SebG3D/TapePuller/docs/servo/servo_mod/servo_mod_6.jpg

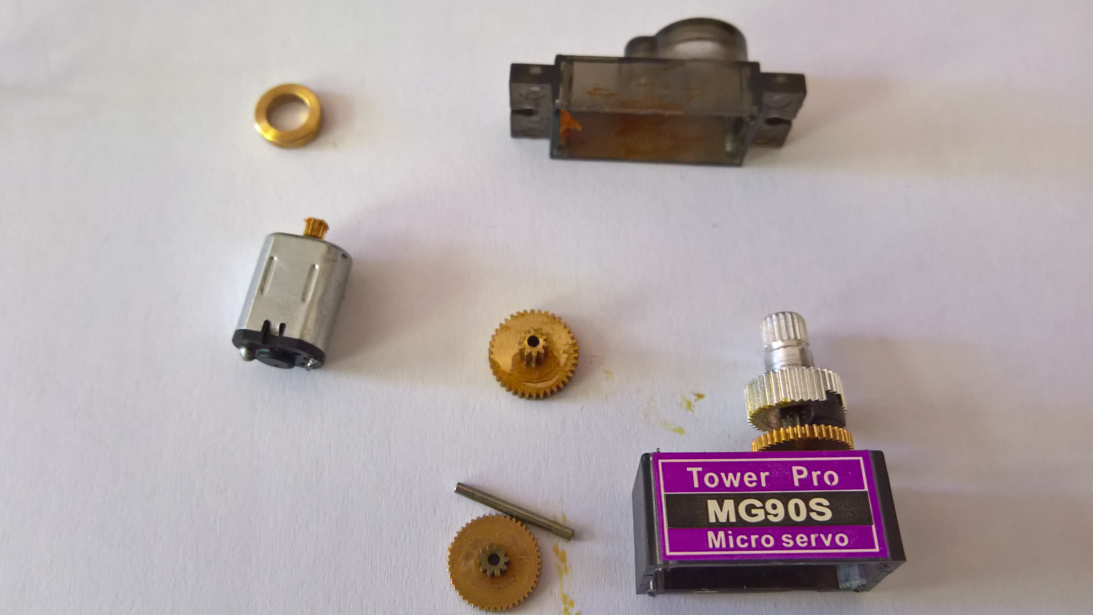
docs/servo/servo_mod/servo_mod_6.jpg
