SebG3D/TapePuller/docs/servo/servo_mod/servo_mod_12.jpg

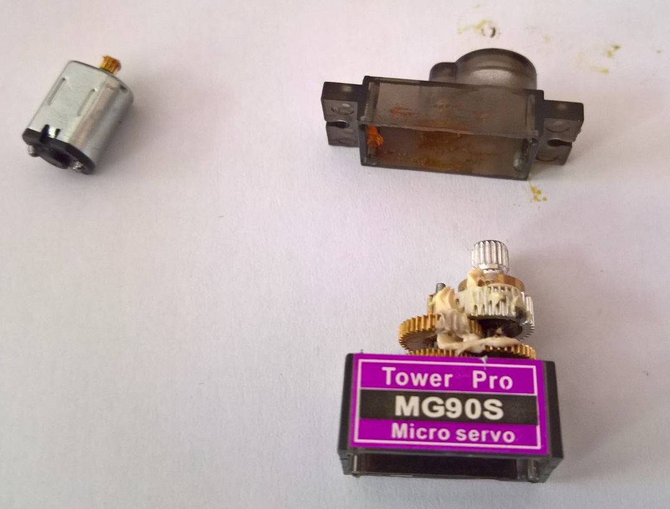
docs/servo/servo_mod/servo_mod_12.jpg
