SebG3D/TapePuller/docs/servo/servo_mod/servo_mod_15.jpg

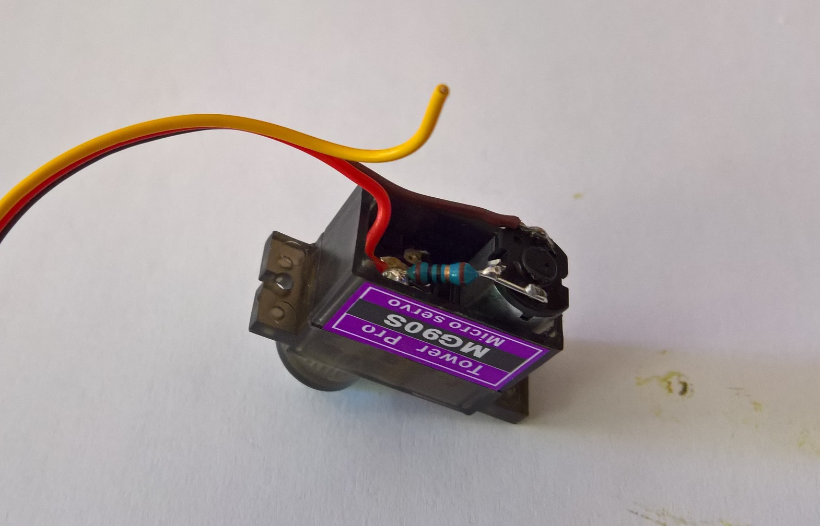
docs/servo/servo_mod/servo_mod_15.jpg
