SebG3D/TapePuller/pictures/Customizer_1.png

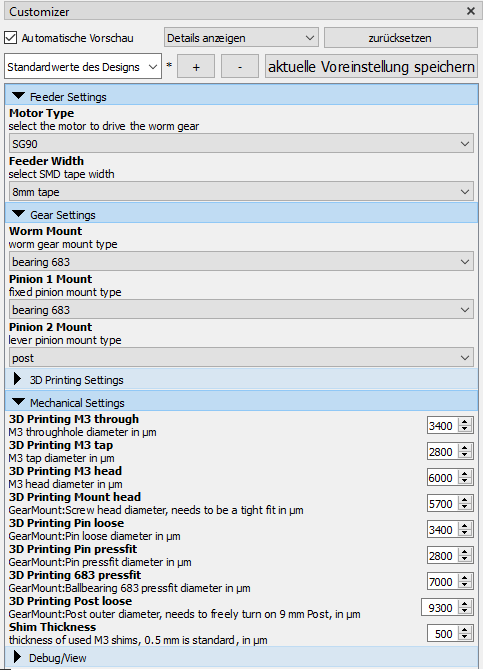
pictures/Customizer_1.png
