SebG3D/TapePuller/pictures/Customizer_2.png

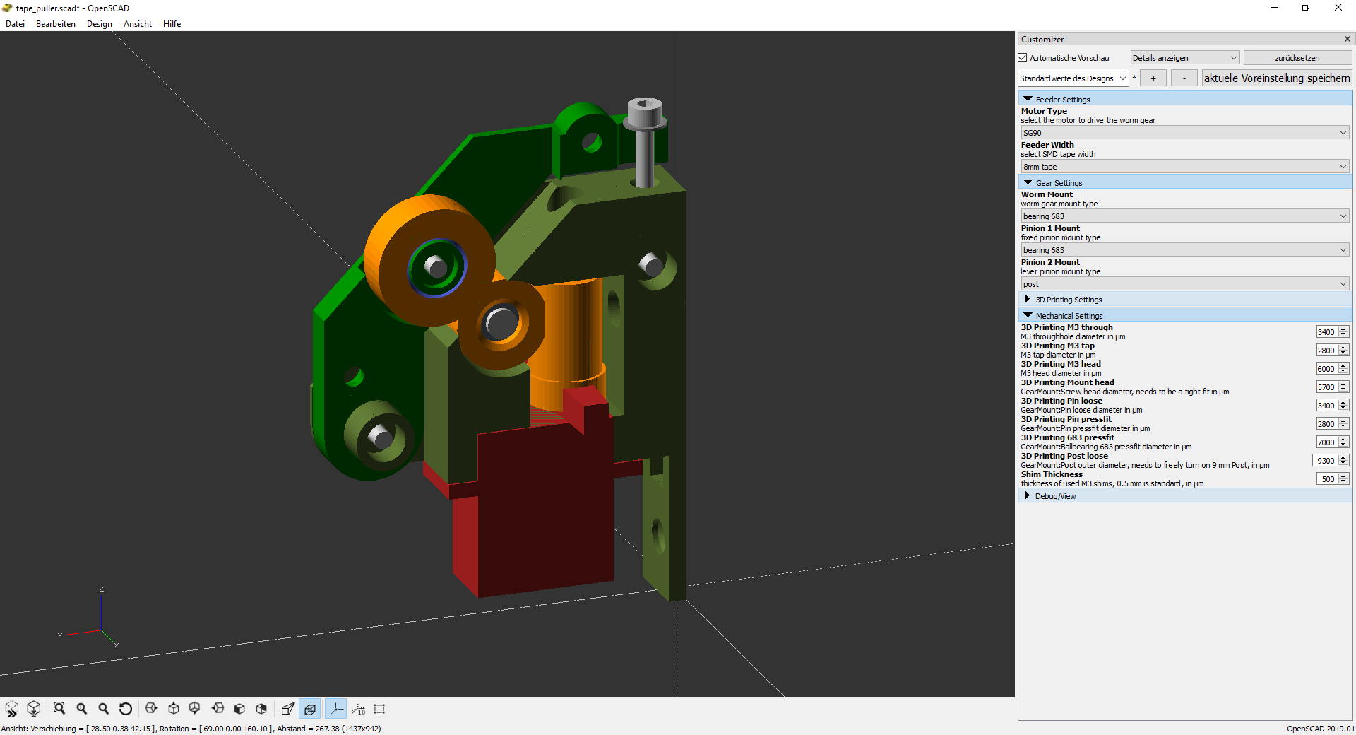
pictures/Customizer_2.png
