SebG3D/TapePuller/pictures/tape_puller_n20.PNG

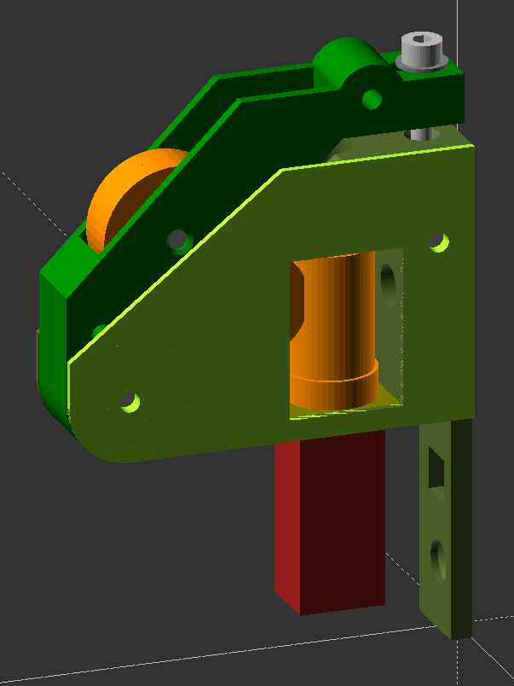
pictures/tape_puller_n20.PNG
