SebG3D/TapePuller/pictures/2019-04-13_First_Test.jpg

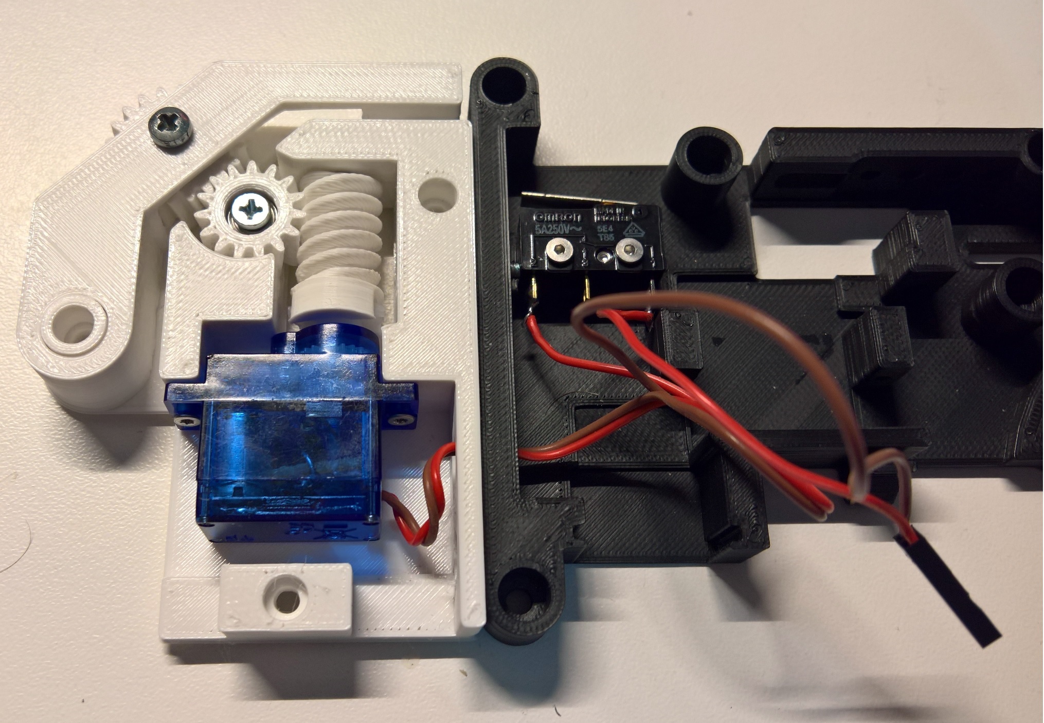
pictures/2019-04-13_First_Test.jpg
